martinroger/ipodesp32/img/a1sMini.png

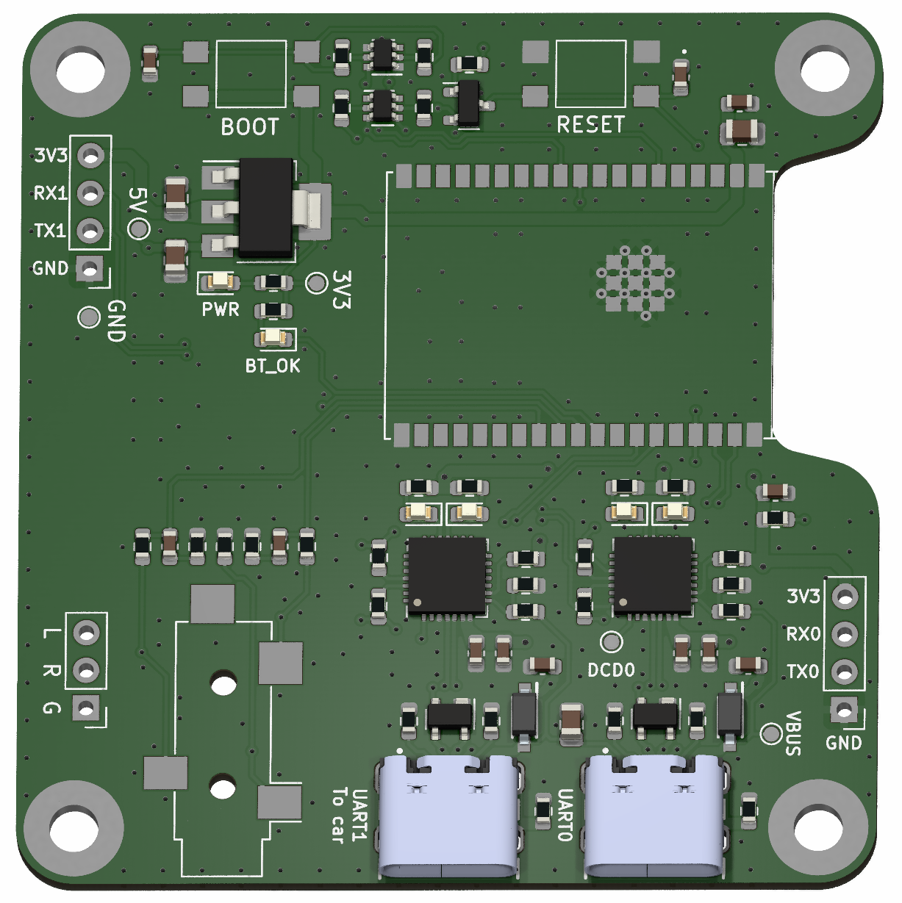
img/a1sMini.png
