martinroger/ipodesp32/img/boostCD.png

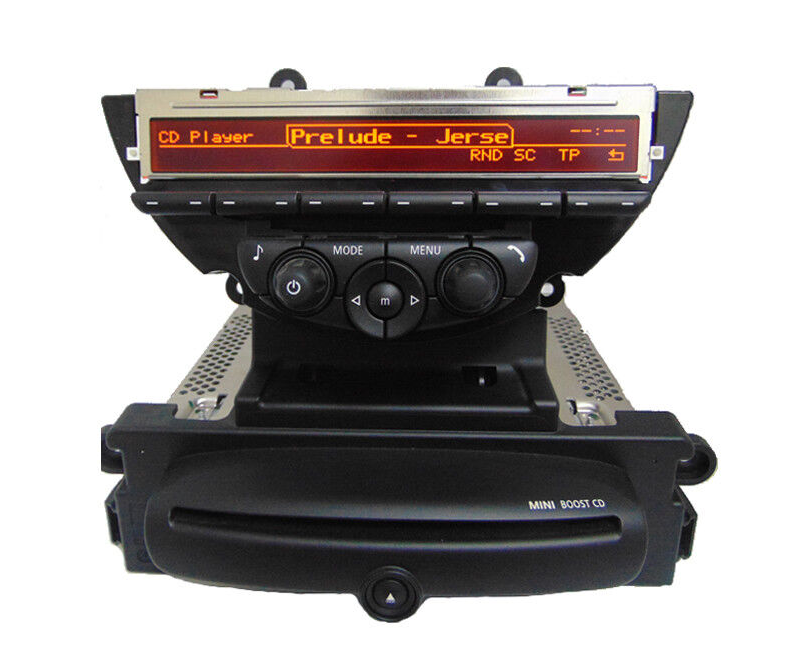
img/boostCD.png
