martinroger/ipodesp32/img/CNT003B.jpg

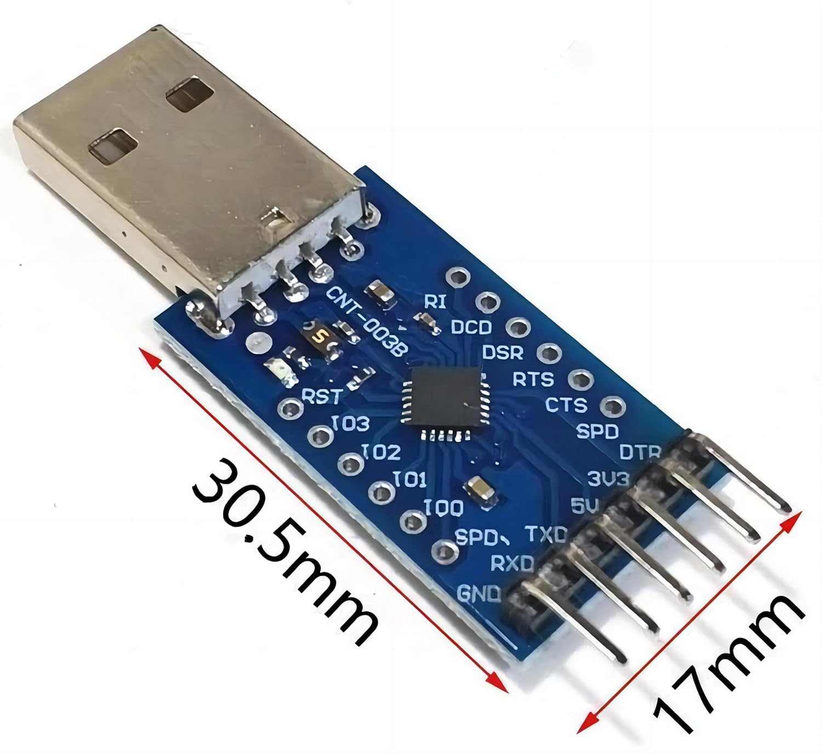
img/CNT003B.jpg
