martinroger/ipodesp32/img/esp32A1SAudioKit.jpg

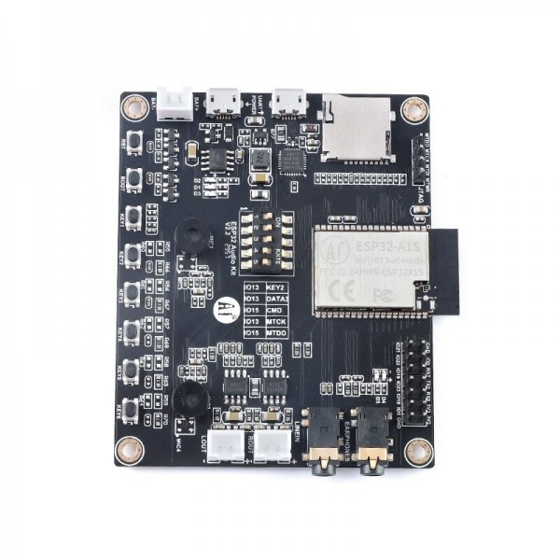
img/esp32A1SAudioKit.jpg
