martinroger/ipodesp32/img/hautDeForme.png

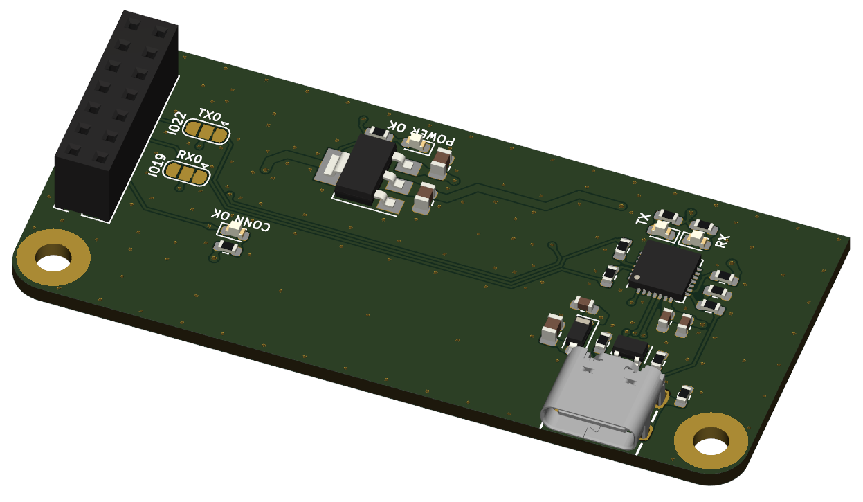
img/hautDeForme.png
