martinroger/ipodesp32/img/LDOBoard.jpg

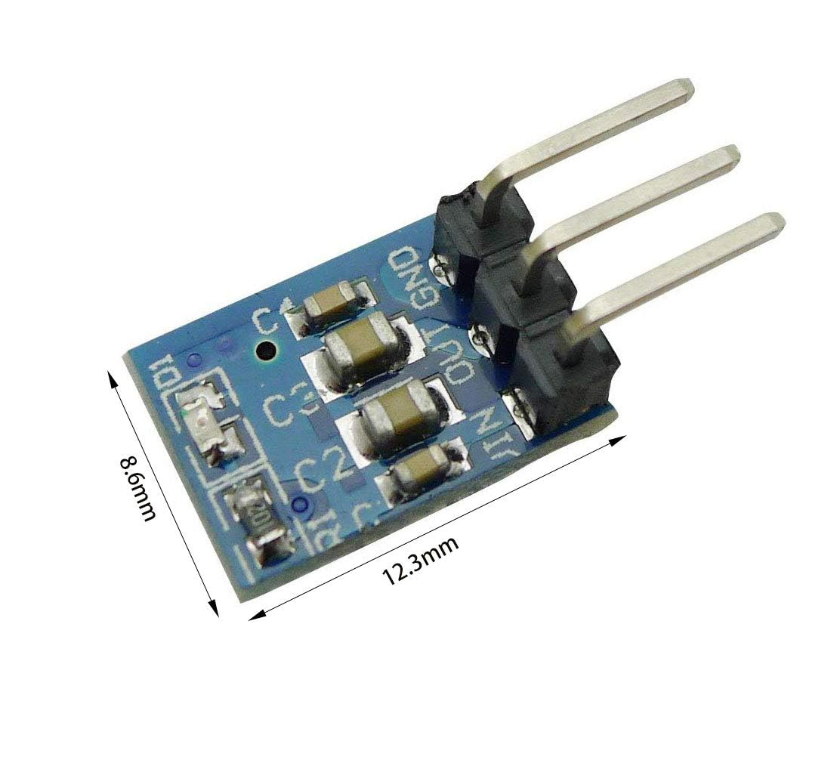
img/LDOBoard.jpg
