martinroger/ipodesp32/img/miniGP2.png

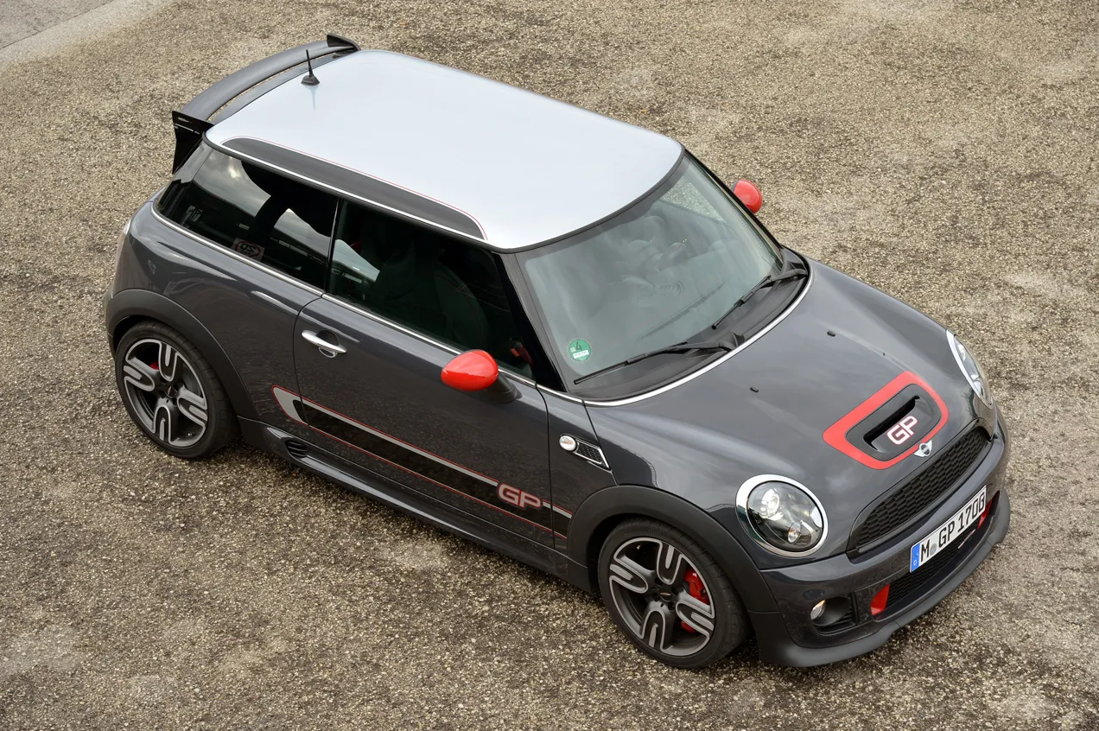
img/miniGP2.png
