martinroger/ipodesp32/img/openWithCode.png

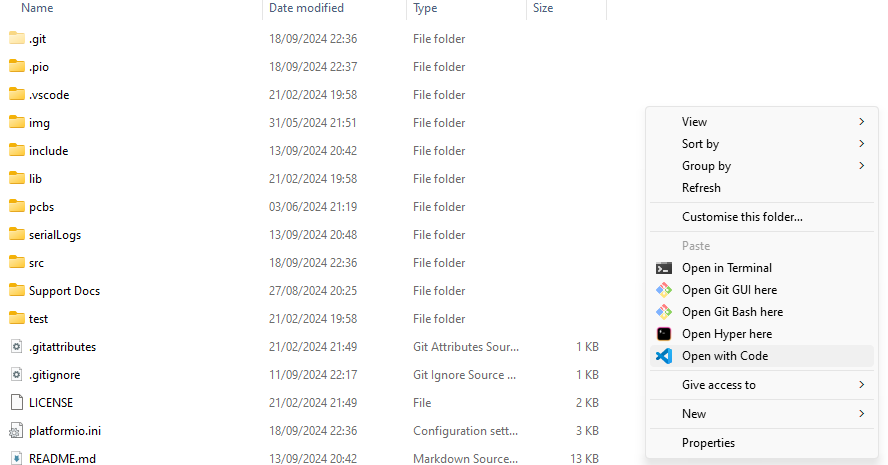
img/openWithCode.png
