martinroger/ipodesp32/img/PL2303.png

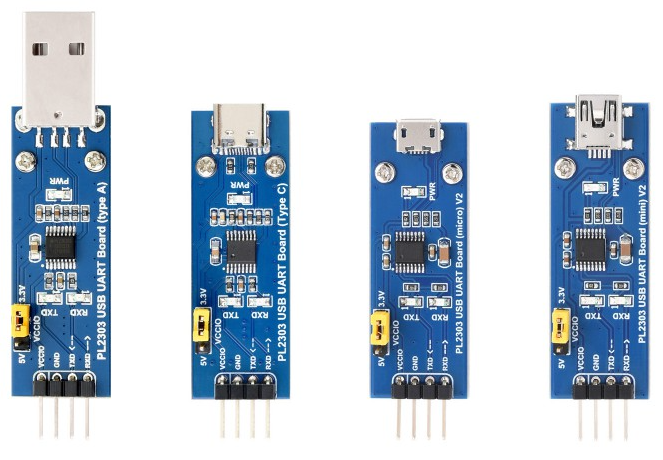
img/PL2303.png
