martinroger/ipodesp32/img/sandwichBoard.png

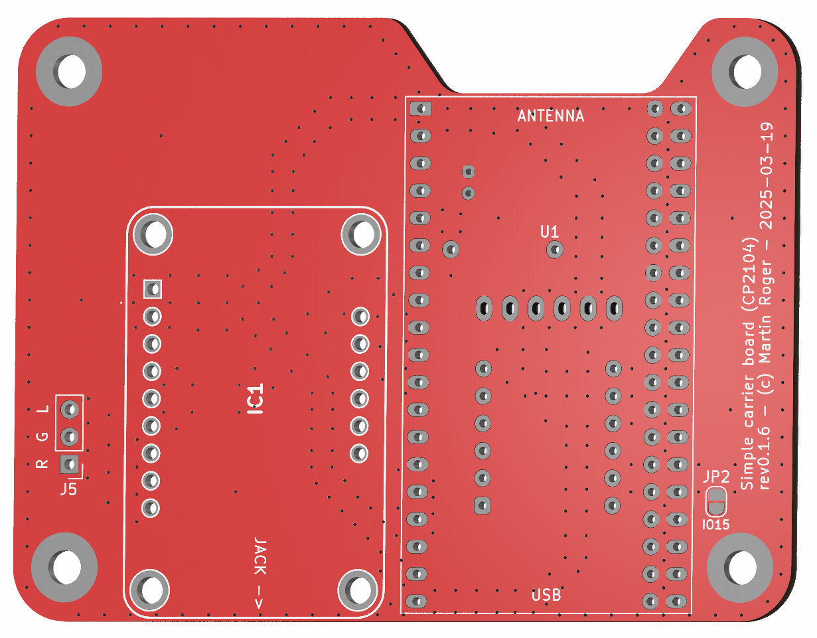
img/sandwichBoard.png
