martinroger/ipodesp32/img/SchemeDevKitCV4.png

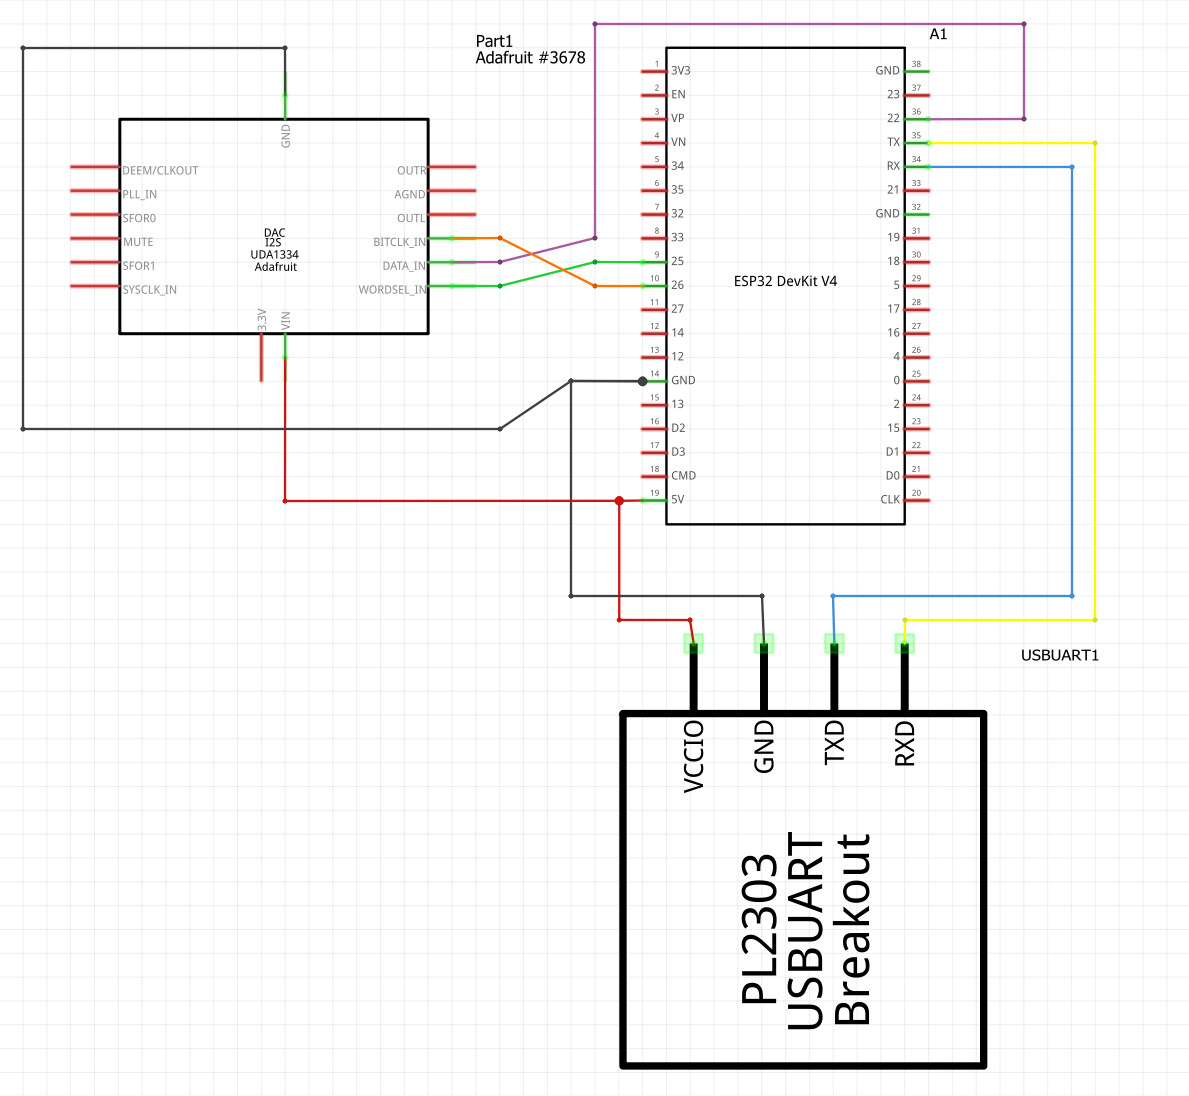
img/SchemeDevKitCV4.png
