martinroger/ipodesp32/img/selectAndUpload.png

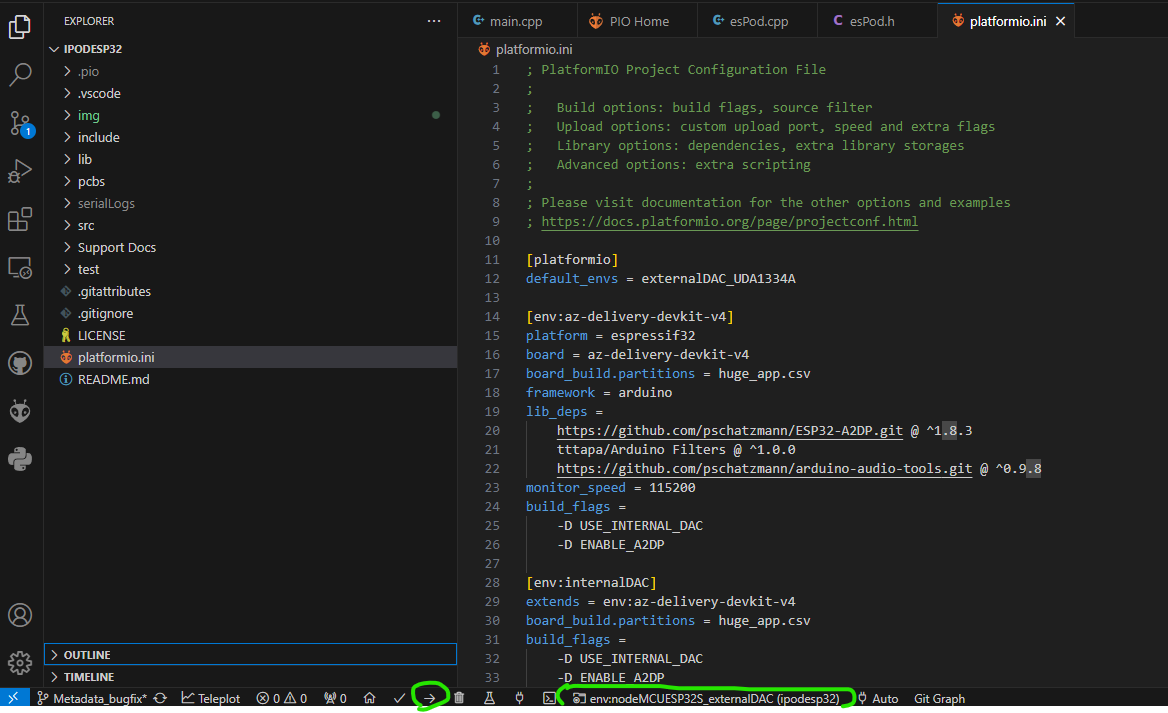
img/selectAndUpload.png
