martinroger/ipodesp32/img/UDA1334A.png

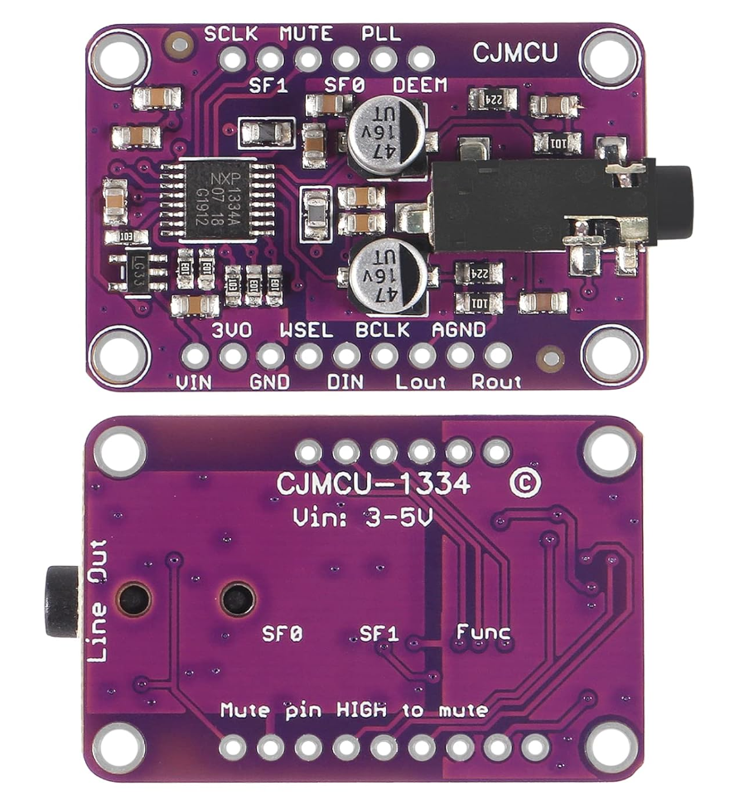
img/UDA1334A.png
